aentinger/TemperatureSensorChildboard/images/temperature-sensor-childboard-top-large.jpg

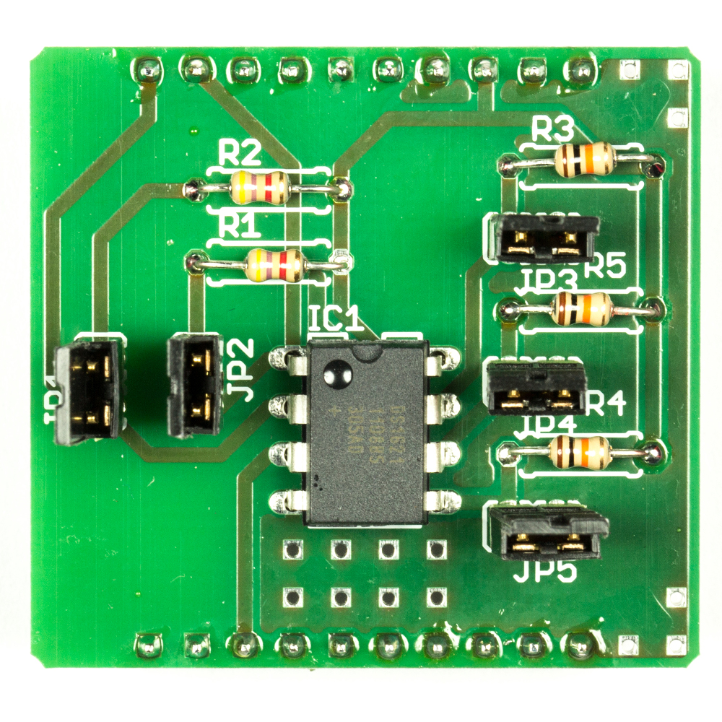
images/temperature-sensor-childboard-top-large.jpg
